greggubben/PhoneHomeBusyBox/images/Controller_Breadboard.jpg

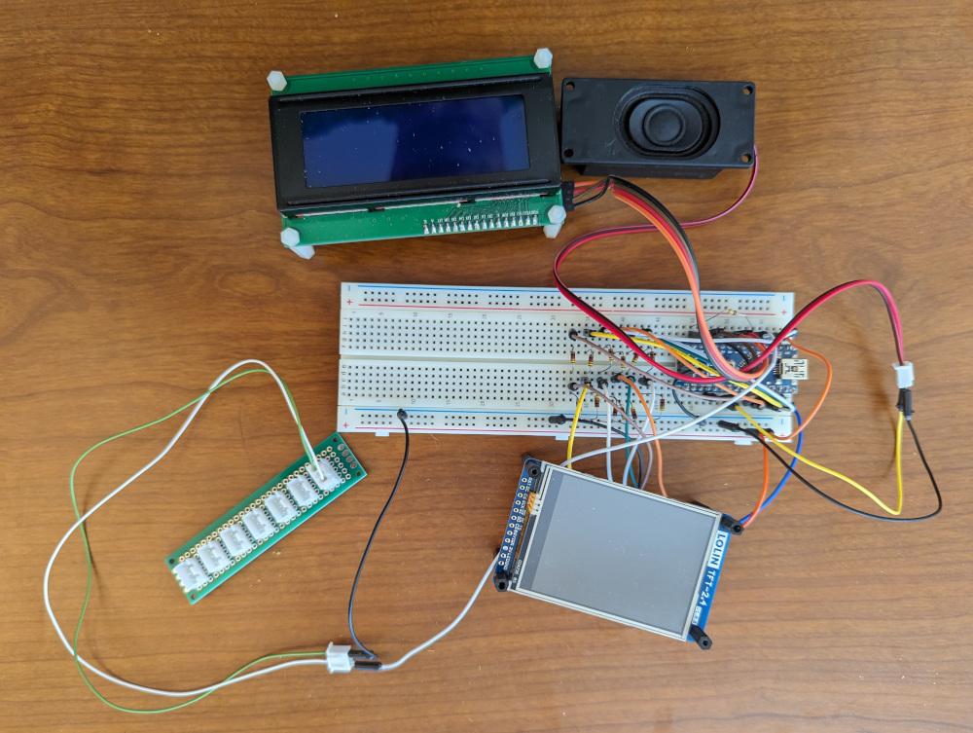
images/Controller_Breadboard.jpg
