greggubben/PhoneHomeBusyBox/images/Controller_Prototype_Bottom.jpg

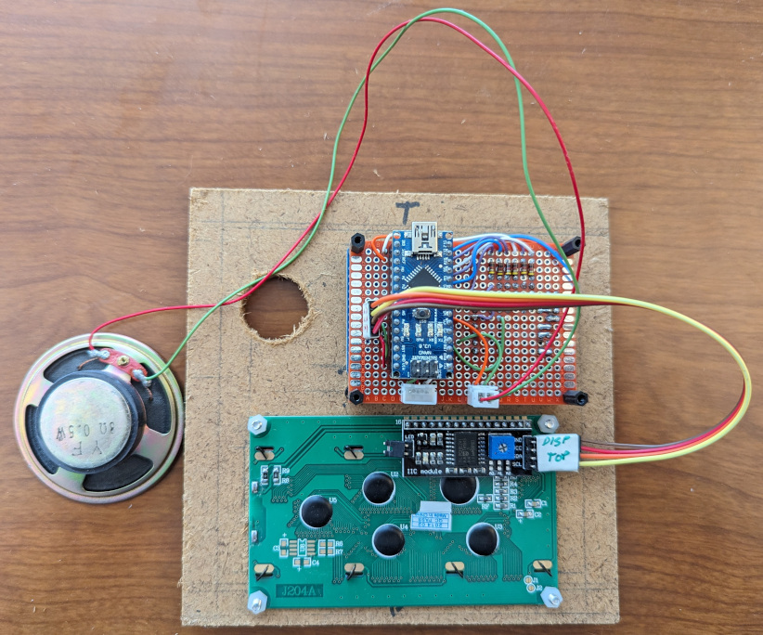
images/Controller_Prototype_Bottom.jpg
