greggubben/PhoneHomeBusyBox/images/Dialer_Breadboard.jpg

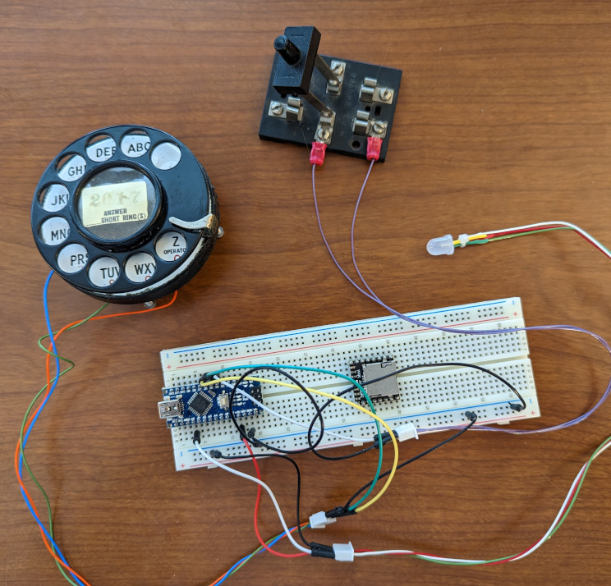
images/Dialer_Breadboard.jpg
