greggubben/PhoneHomeBusyBox/images/Dialer_Prototype_Bottom.jpg

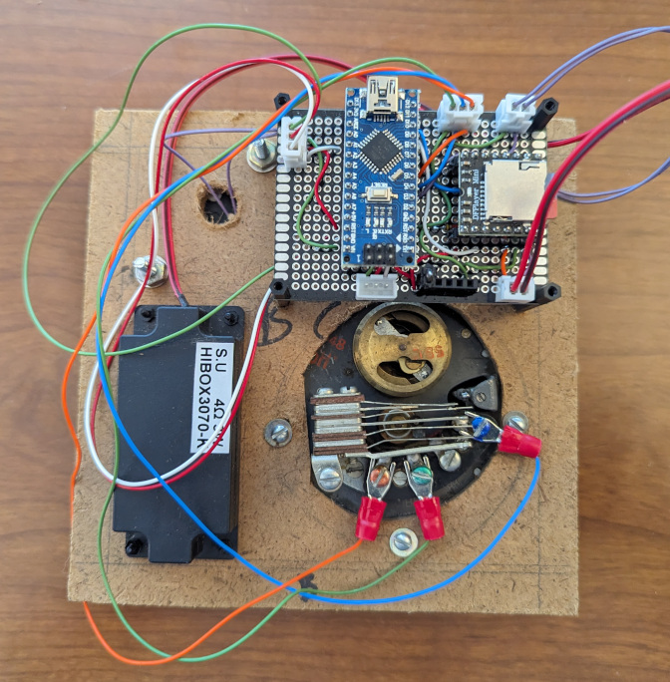
images/Dialer_Prototype_Bottom.jpg
