greggubben/PhoneHomeBusyBox/images/Dialer_Schematic.jpg

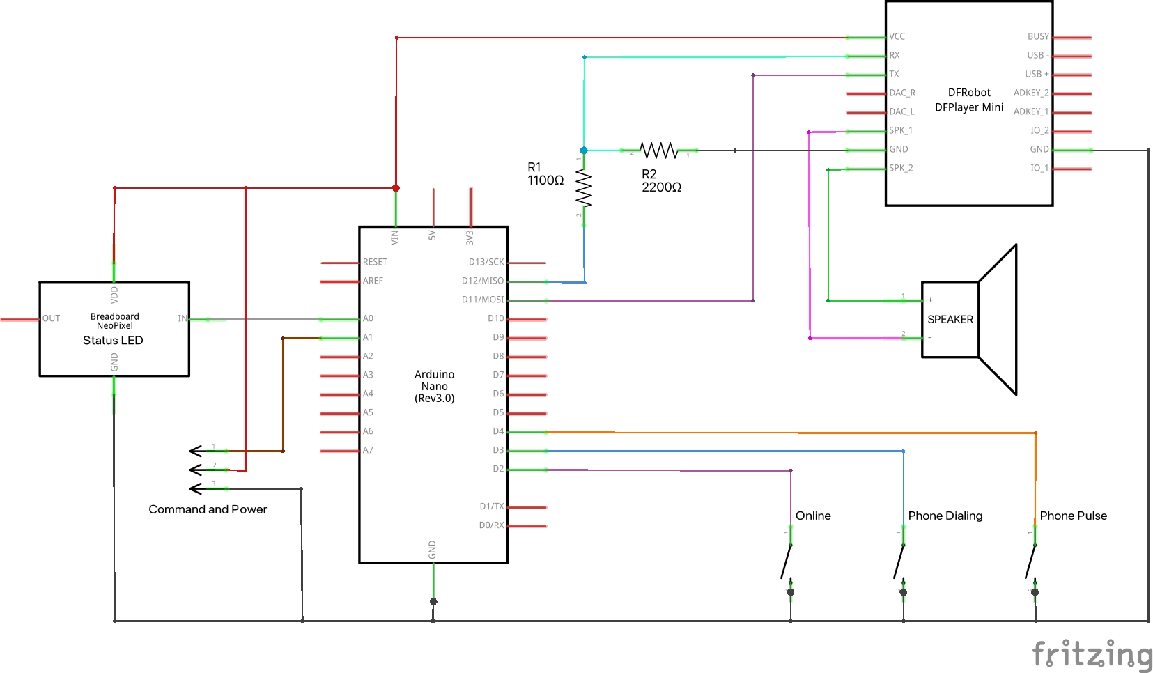
images/Dialer_Schematic.jpg
