greggubben/PhoneHomeBusyBox/images/FlipBits_Prototype_Bottom.jpg

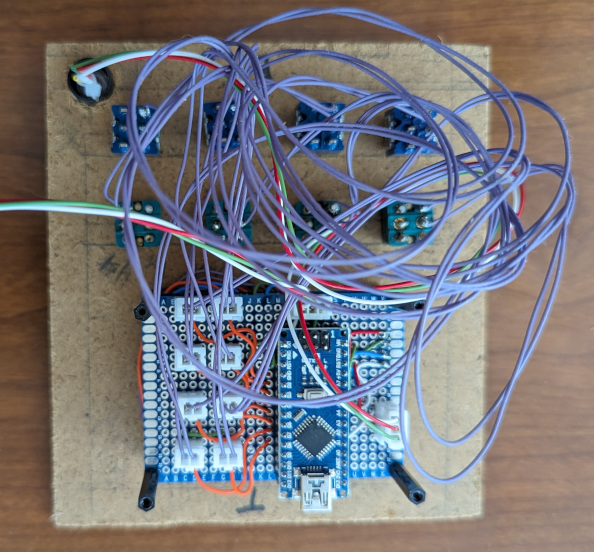
images/FlipBits_Prototype_Bottom.jpg
