greggubben/PhoneHomeBusyBox/images/HookMeUp_Prototype_Bottom.jpg

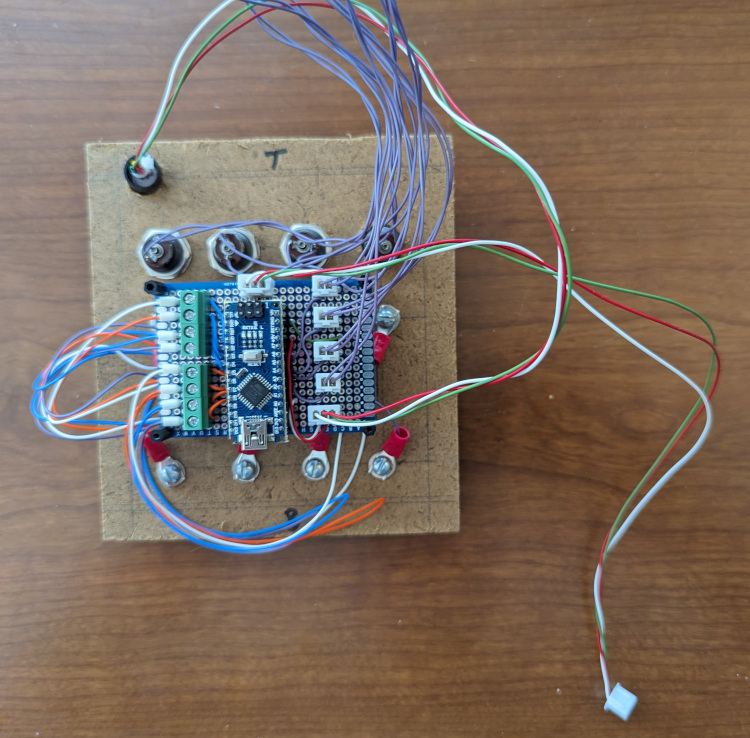
images/HookMeUp_Prototype_Bottom.jpg
