greggubben/PhoneHomeBusyBox/images/Slider_Prototype_Bottom.jpg

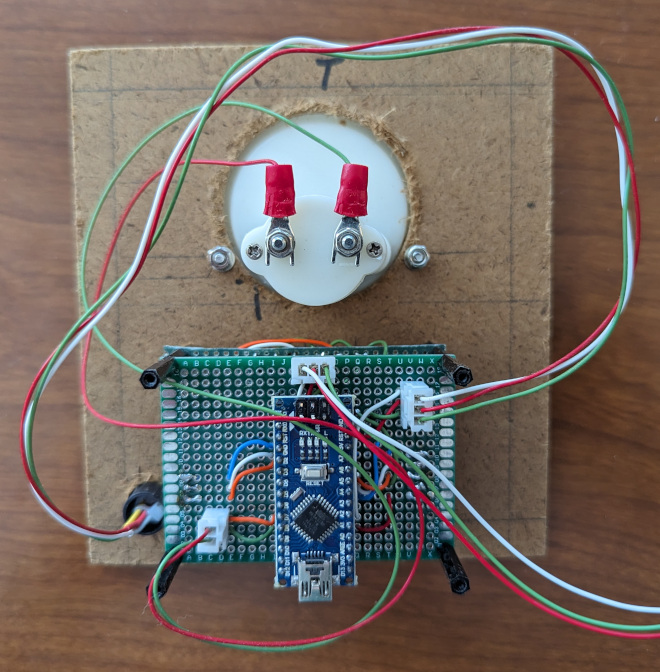
images/Slider_Prototype_Bottom.jpg
