greggubben/PhoneHomeBusyBox/images/SpinDigit_Breadboard.jpg

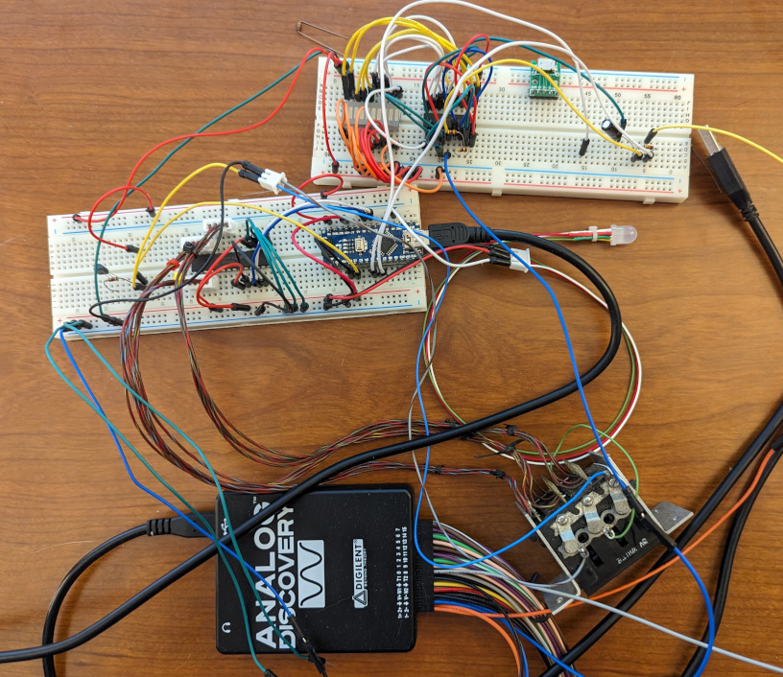
images/SpinDigit_Breadboard.jpg
