greggubben/PhoneHomeBusyBox/images/SpinDigit_Prototype_Bottom.jpg

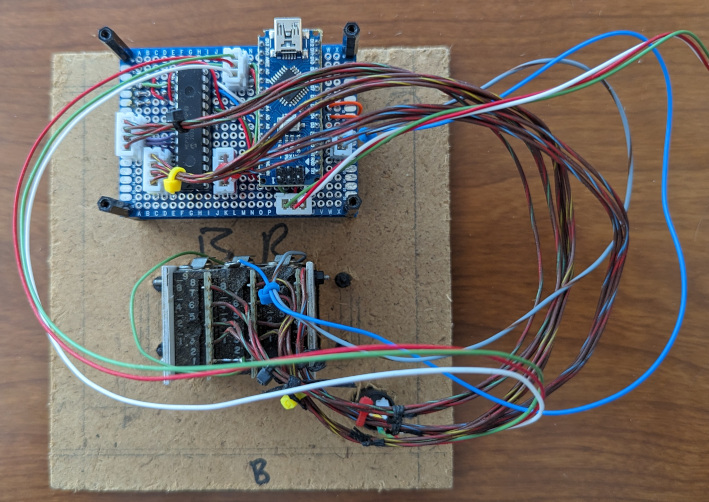
images/SpinDigit_Prototype_Bottom.jpg
