greggubben/PhoneHomeBusyBox/images/Controller_Soldered_Top.jpg

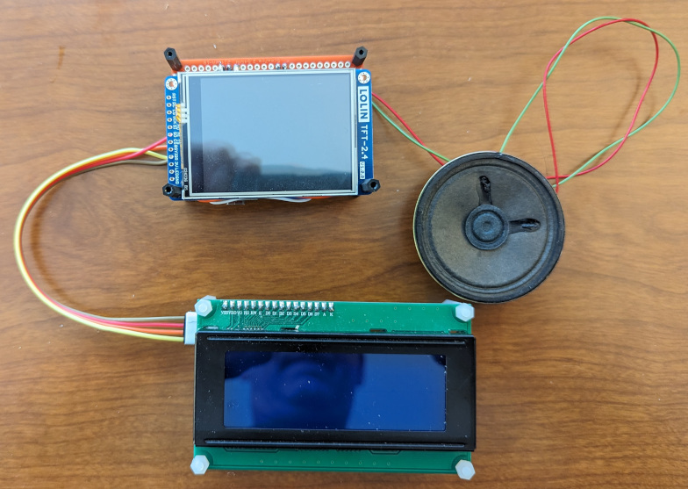
images/Controller_Soldered_Top.jpg
