greggubben/PhoneHomeBusyBox/Controller/Entertainer.h

/*
Notes to play the Entertainer by Scott Joplin
*/

Note entertainer[] = {
  {NOTE_D3, EIGHTH},
  {NOTE_DS3,EIGHTH},
  {NOTE_E3, EIGHTH},
  {NOTE_C4, QUARTER},
  {NOTE_E3, EIGHTH},
  {NOTE_C4, QUARTER},
  {NOTE_E3, EIGHTH},
  {NOTE_C4, DOTTEDHALF},
  {NOTE_C4, EIGHTH},
  {NOTE_D4, EIGHTH},
  {NOTE_DS4,EIGHTH},
  {NOTE_E4, EIGHTH},
  {NOTE_C4, EIGHTH},
  {NOTE_D4, EIGHTH},
  {NOTE_E4, QUARTER},
  {NOTE_C4, EIGHTH},
  {NOTE_D4, QUARTER},
  {NOTE_C4, HALF},
  {END_NOTES,  END_NOTES}
};
/*
  {REST,    QUARTER},
  {NOTE_D3, EIGHTH},
  {NOTE_DS3,EIGHTH},
  {NOTE_E3, EIGHTH},
  {NOTE_C4, QUARTER},
  {NOTE_E3, EIGHTH},
  {NOTE_C4, QUARTER},
  {NOTE_E3, EIGHTH},
  {NOTE_C4, DOTTEDHALF},
  {NOTE_A3, EIGHTH},
  {NOTE_G3, EIGHTH},
  {NOTE_FS3, EIGHTH},
  {NOTE_A3,  EIGHTH},
  {NOTE_C4,  EIGHTH},
  {NOTE_E4,  QUARTER},
  {NOTE_D4,  EIGHTH},
  {NOTE_C4,  EIGHTH},
  {NOTE_A3,  EIGHTH},
  {NOTE_D4,  HALF},
  {REST,    QUARTER},
  {NOTE_D3, EIGHTH},
  {NOTE_DS3,EIGHTH},
  {NOTE_E3, EIGHTH},
  {NOTE_C4, QUARTER},
  {NOTE_E3, EIGHTH},
  {NOTE_C4, QUARTER},
  {NOTE_E3, EIGHTH},
  {NOTE_C4, DOTTEDHALF},
  {NOTE_C4, EIGHTH},
  {NOTE_D4, EIGHTH},
  {NOTE_DS4,EIGHTH},
  {NOTE_E4, EIGHTH},
  {NOTE_C4, EIGHTH},
  {NOTE_D4, EIGHTH},
  {NOTE_E4, QUARTER},
  {NOTE_C4, EIGHTH},
  {NOTE_D4, QUARTER},
  {NOTE_C4, DOTTEDHALF},
  {NOTE_C4, EIGHTH},
  {NOTE_D4,  EIGHTH},
  {NOTE_E4,  EIGHTH},
  {NOTE_C4,  EIGHTH},
  {NOTE_D4,  EIGHTH},
  {NOTE_E4,  QUARTER},
  {NOTE_C4,  EIGHTH},
  {NOTE_D4,  EIGHTH},
  {NOTE_C4,  EIGHTH},
  {NOTE_E4,  EIGHTH},
  {NOTE_C4,  EIGHTH},
  {NOTE_D4,  EIGHTH},
  {NOTE_E4,  QUARTER},
  {NOTE_C4,  EIGHTH},
  {NOTE_D4,  EIGHTH},
  {NOTE_C4,  EIGHTH},
  {NOTE_E4,  EIGHTH},
  {NOTE_C4,  EIGHTH},
  {NOTE_D4,  EIGHTH},
  {NOTE_E4,  QUARTER},
  {NOTE_C4,  EIGHTH},
  {NOTE_D4,  QUARTER},
  {NOTE_C4,  HALF},
  {NOTE_E4,  QUARTER},
  {END_NOTES,  END_DUR}
};
*/
