greggubben/PhoneHomeBusyBox/PhoneHomeLib/PhoneHome_Definitions.h

/*!
 * Phone Home Briefcase Game common definitions
 *
 * Common file for definitions to be used by all modules in the game.
 */

#ifndef PHONEHOME_DEFINITIONS_H
#define PHONEHOME_DEFINITIONS_H

#include <Arduino.h>


// Define common pins
#define RANDOM_SEED_PIN A7
#define STATUS_LED_PIN A0
#define PJON_COMM_PIN A1


#endif // PHONEHOME_DEFINITIONS_H
